Tangdor/BDA_Project/BDA/bda.jpg

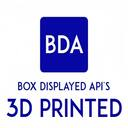
BDA/bda.jpg
