Tangdor/BDA_Project/BDA/calendar.jpg

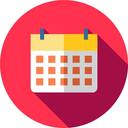
BDA/calendar.jpg
