Tangdor/BDA_Project/BDA/cars.jpg

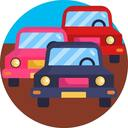
BDA/cars.jpg
