Tangdor/BDA_Project/BDA/corona.jpg

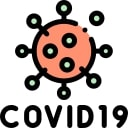
BDA/corona.jpg
