Tangdor/BDA_Project/BDA/mailed.jpg

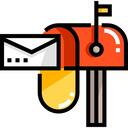
BDA/mailed.jpg
