Tangdor/BDA_Project/BDA/train.jpg

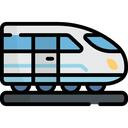
BDA/train.jpg
