Tangdor/BDA_Project/BDA/trophyO.jpg

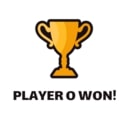
BDA/trophyO.jpg
