Tangdor/BDA_Project/BDA/trophyX.jpg

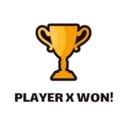
BDA/trophyX.jpg
