Tangdor/BDA_Project/BDA/weather.jpg

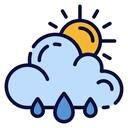
BDA/weather.jpg
