Tangdor/BDA_Project/BDA/weatherBrokenClouds.jpg

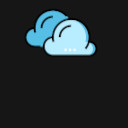
BDA/weatherBrokenClouds.jpg
