Tangdor/BDA_Project/BDA/weatherClearSky.jpg

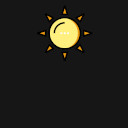
BDA/weatherClearSky.jpg
