Tangdor/BDA_Project/BDA/weatherFewClouds.jpg

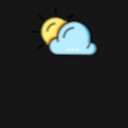
BDA/weatherFewClouds.jpg
