Tangdor/BDA_Project/BDA/weatherMist.jpg

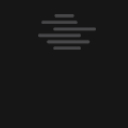
BDA/weatherMist.jpg
