Tangdor/BDA_Project/BDA/weatherSnow.jpg

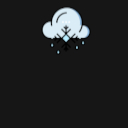
BDA/weatherSnow.jpg
