Tangdor/BDA_Project/BDA/zimmertemperatur.jpg

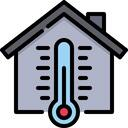
BDA/zimmertemperatur.jpg
